R-Cuculiere/2021_2022_CAPTEUR_PEREUR_CUCULIERE/ELECTRONIQUE_ANALOGIQUE_SIMLUATIONS/Schéma_solution_Ampli_Transimpédance.asc

C1: cap; 100n
C2: cap; 100n
C3: cap; 100n
C4: cap; 1µ
R1: res; 100k
R2: res; 1k
R3: res; 100k
R5: res; 10k
R6: res; 1k
U1: LTC1050
V1: voltage; 5
V2: voltage; PULSE(0 1 0.2 0.1 0.1 20)
X1: Schéma_simulation_capteur
Named nets: 0, +5V, ADC
.tran 2
;ac dec 200 1 1G
