R-Cuculiere/2021_2022_CAPTEUR_PEREUR_CUCULIERE/ELECTRONIQUE_ANALOGIQUE_SIMLUATIONS/capteur.asc

B1: current; I=V(cp,cn)*(10n+(v(gc,gn)*10n))
C1: cap
R1: res
Named nets: gn, gp, gc, cp, cn
.tran 20
