R-Cuculiere/2021_2022_CAPTEUR_PEREUR_CUCULIERE/PGM_Arduino/TP4_Pong_PotentiometreNunchuck/TP4_Pong_Potentiometre&Nunchuck/Arduino/PotentiometrePong_Arduino/PotentiometrePong_Arduino.ino

/* PotSend
 *  Send analog values from pots or similar over the serial port
 *  Also see:  http://www.arduino.cc/en/Tutorial/Graph
 */

int potPin = 0;

void setup() {
  Serial.begin(19200);
}

void loop() {
  int val = analogRead(potPin);
  val = val/4;
//  Serial.write(val, BYTE);
  Serial.write(val);
  delay(100);
}
